Nailim/shuttler/Code/Python/TelemetryProcessing/telemetry2video/Attitude/resources/center.png

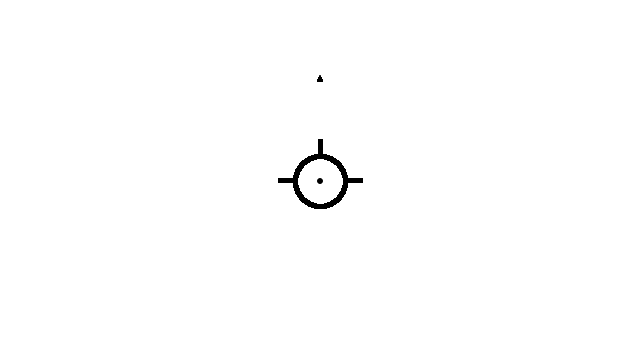
Code/Python/TelemetryProcessing/telemetry2video/Attitude/resources/center.png
