Nailim/shuttler/Code/Python/TelemetryProcessing/telemetry2video/Attitude/resources_opencv/center.png

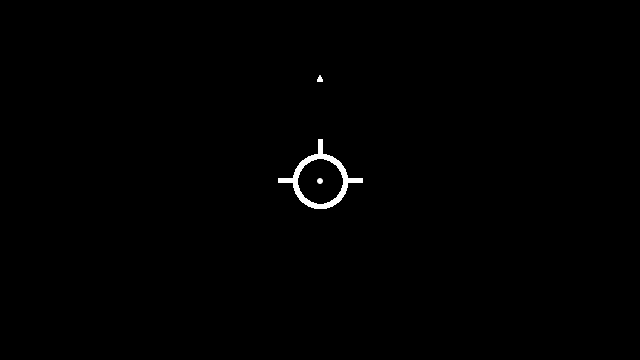
Code/Python/TelemetryProcessing/telemetry2video/Attitude/resources_opencv/center.png
