Nailim/shuttler/Code/Python/TelemetryProcessing/telemetry2video/Attitude/resources_opencv/terrain.png

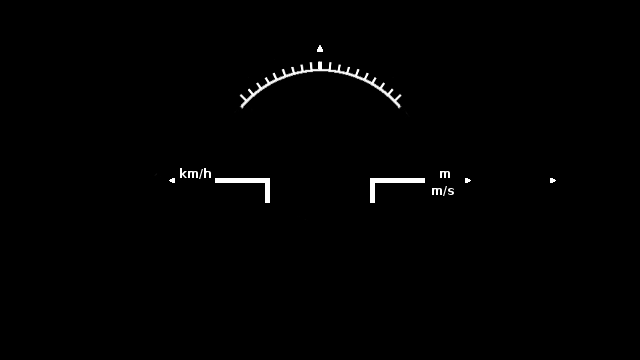
Code/Python/TelemetryProcessing/telemetry2video/Attitude/resources_opencv/terrain.png
